dektronics/printalyzer-uvdensitometer/software/firmware/src/state_display.c

#include "state_display.h"

#define LOG_TAG "state_display"

#include <stdbool.h>
#include <math.h>
#include <elog.h>

#include "keypad.h"
#include "display.h"
#include "light.h"
#include "task_sensor.h"
#include "densitometer.h"
#include "settings.h"
#include "util.h"

typedef struct {
    state_t base;
    bool vis_uv;
    bool display_dirty;
    bool light_dirty;
    bool is_detect_prev;
    bool light_idle_on;
    uint32_t light_idle_timeout;
    uint32_t light_idle_off_ticks;
    bool menu_pending;
    int up_repeat;
    int down_repeat;
    state_identifier_t measure_state;
    state_identifier_t alternate_state;
    densitometer_t *densitometer;
    const char *display_title;
    display_mode_t display_mode;
} state_display_t;

static void state_display_entry(state_t *state_base, state_controller_t *controller, state_identifier_t prev_state);
static void state_reflection_display_entry(state_t *state_base, state_controller_t *controller, state_identifier_t prev_state);
static void state_transmission_display_entry(state_t *state_base, state_controller_t *controller, state_identifier_t prev_state);

static void state_display_process(state_t *state_base, state_controller_t *controller);

static state_display_t state_vis_reflection_display_data = {
    .base = {
        .state_entry = state_reflection_display_entry,
        .state_process = state_display_process,
        .state_exit = NULL
    },
    .vis_uv = true,
    .display_dirty = true,
    .light_dirty = true,
    .is_detect_prev = false,
    .light_idle_on = false,
    .light_idle_timeout = 0,
    .light_idle_off_ticks = 0,
    .menu_pending = false,
    .up_repeat = 0,
    .down_repeat = 0,
    .measure_state = STATE_VIS_REFLECTION_MEASURE,
    .alternate_state = STATE_VIS_TRANSMISSION_DISPLAY,
    .densitometer = NULL,
    .display_title = "Reflection",
    .display_mode = DISPLAY_MODE_VIS_REFLECTION
};

static state_display_t state_vis_transmission_display_data = {
    .base = {
        .state_entry = state_transmission_display_entry,
        .state_process = state_display_process,
        .state_exit = NULL
    },
    .vis_uv = true,
    .display_dirty = true,
    .light_dirty = true,
    .is_detect_prev = false,
    .light_idle_on = false,
    .light_idle_timeout = 0,
    .light_idle_off_ticks = 0,
    .menu_pending = false,
    .up_repeat = 0,
    .down_repeat = 0,
    .measure_state = STATE_VIS_TRANSMISSION_MEASURE,
    .alternate_state = STATE_UV_TRANSMISSION_DISPLAY,
    .densitometer = NULL,
    .display_title = "Transmission",
    .display_mode = DISPLAY_MODE_VIS_TRANSMISSION
};

static state_display_t state_uv_transmission_display_data = {
    .base = {
        .state_entry = state_transmission_display_entry,
        .state_process = state_display_process,
        .state_exit = NULL
    },
    .vis_uv = false,
    .display_dirty = true,
    .light_dirty = true,
    .is_detect_prev = false,
    .light_idle_on = false,
    .light_idle_timeout = 0,
    .light_idle_off_ticks = 0,
    .menu_pending = false,
    .up_repeat = 0,
    .down_repeat = 0,
    .measure_state = STATE_UV_TRANSMISSION_MEASURE,
    .alternate_state = STATE_VIS_REFLECTION_DISPLAY,
    .densitometer = NULL,
    .display_title = "Transmission",
    .display_mode = DISPLAY_MODE_UV_TRANSMISSION
};

state_t *state_vis_reflection_display()
{
    return (state_t *)&state_vis_reflection_display_data;
}

state_t *state_vis_transmission_display()
{
    return (state_t *)&state_vis_transmission_display_data;
}

state_t *state_uv_transmission_display()
{
    return (state_t *)&state_uv_transmission_display_data;
}

void state_display_entry(state_t *state_base, state_controller_t *controller, state_identifier_t prev_state)
{
    state_display_t *state = (state_display_t *)state_base;

    state->display_dirty = true;
    state->light_dirty = true;
    state->is_detect_prev = false;
    state->light_idle_on = false;
    state->light_idle_off_ticks = 0;
    state->menu_pending = false;
    state->up_repeat = 0;
    state->down_repeat = 0;

    settings_user_idle_light_t idle_light;
    settings_get_user_idle_light(&idle_light);
    state->light_idle_timeout = 1000UL * idle_light.timeout;

    state_controller_set_home_state(controller, state_controller_get_current_state(controller));
}

void state_reflection_display_entry(state_t *state_base, state_controller_t *controller, state_identifier_t prev_state)
{
    state_display_entry(state_base, controller, prev_state);

    state_display_t *state = (state_display_t *)state_base;
    state->densitometer = densitometer_vis_reflection();

    if (prev_state == STATE_VIS_REFLECTION_MEASURE) {
        /* Set idle light state upon entry assuming measurement is similar to detect */
        if (state->light_idle_timeout > 0) {
            state->light_idle_on = true;
            state->light_idle_off_ticks = osKernelGetTickCount() + state->light_idle_timeout;
        } else {
            state->light_idle_on = false;
            state->light_idle_off_ticks = 0;
        }
        state->light_dirty = true;
    }
}

void state_transmission_display_entry(state_t *state_base, state_controller_t *controller, state_identifier_t prev_state)
{
    state_display_entry(state_base, controller, prev_state);

    state_display_t *state = (state_display_t *)state_base;
    state->densitometer = state->vis_uv ? densitometer_vis_transmission() : densitometer_uv_transmission();

    if (prev_state == (state->vis_uv ? STATE_VIS_TRANSMISSION_MEASURE : STATE_UV_TRANSMISSION_MEASURE)) {
        /* Set idle light state upon entry assuming measurement is similar to detect */
        if (state->light_idle_timeout > 0) {
            state->light_idle_on = true;
            state->light_idle_off_ticks = osKernelGetTickCount() + state->light_idle_timeout;
        } else {
            state->light_idle_on = false;
            state->light_idle_off_ticks = 0;
        }
        state->light_dirty = true;
    }
}

void state_display_process(state_t *state_base, state_controller_t *controller)
{
    state_display_t *state = (state_display_t *)state_base;
    bool is_detect = keypad_is_detect();

    /* Update idle light properties based on a detect switch change */
    if (is_detect != state->is_detect_prev) {
        state->is_detect_prev = is_detect;

        if (is_detect && !state->light_idle_on) {
            state->light_idle_on = true;
            state->light_idle_off_ticks = 0;
            state->light_dirty = true;
        } else if (!is_detect && state->light_idle_on) {
            if (state->light_idle_timeout > 0) {
                state->light_idle_off_ticks = osKernelGetTickCount() + state->light_idle_timeout;
            } else {
                state->light_idle_on = false;
                state->light_idle_off_ticks = 0;
            }
            state->light_dirty = true;
        }
    }

    /* Check for idle light timeout */
    if (state->light_idle_on && state->light_idle_off_ticks > 0
        && TIME_AFTER(osKernelGetTickCount(), state->light_idle_off_ticks)) {
        state->light_idle_on = false;
        state->light_idle_off_ticks = 0;
        state->light_dirty = true;
    }

    /* Apply idle light change */
    if (state->light_dirty) {
        densitometer_set_idle_light(state->densitometer, state->light_idle_on);
        state->light_dirty = false;
    }

    keypad_event_t keypad_event;
    if (keypad_wait_for_event(&keypad_event, STATE_KEYPAD_WAIT) == osOK) {
        state->display_dirty = true;

        if (state->menu_pending) {
            if ((keypad_event.keypad_state & (KEYPAD_BUTTON_UP | KEYPAD_BUTTON_DOWN)) == 0) {
                state->menu_pending = false;
                state_controller_set_next_state(controller, STATE_MAIN_MENU);
            }
        } else {
            if (is_detect && keypad_is_only_key_pressed(&keypad_event, KEYPAD_BUTTON_ACTION)) {
                state_controller_set_next_state(controller, state->measure_state);
            } else if (keypad_event.key == KEYPAD_BUTTON_UP) {
                if (keypad_event.pressed || keypad_event.repeated) {
                    if (state->up_repeat < 5) {
                        state->up_repeat++;
                    } else if (state->up_repeat == 5) {
                        log_i("Clear zero measurement");
                        densitometer_set_zero_d(state->densitometer, NAN);
                        state->up_repeat++;
                        state->display_dirty = true;
                    }
                } else {
                    state->up_repeat = 0;
                    state->display_dirty = true;
                }
            } else if (keypad_event.key == KEYPAD_BUTTON_DOWN) {
                if (keypad_event.pressed || keypad_event.repeated) {
                    if (state->down_repeat < 5) {
                        state->down_repeat++;
                    } else if (state->down_repeat == 5) {
                        log_i("Setting zero measurement");
                        float last_reading = densitometer_get_reading_d(state->densitometer);
                        densitometer_set_zero_d(state->densitometer, last_reading);
                        state->down_repeat++;
                        state->display_dirty = true;
                    }
                } else {
                    state->down_repeat = 0;
                    state->display_dirty = true;
                }
            } else if (keypad_is_only_key_pressed(&keypad_event, KEYPAD_BUTTON_MENU)) {
                state_controller_set_next_state(controller, state->alternate_state);
            }

            if (keypad_is_key_combo_pressed(&keypad_event, KEYPAD_BUTTON_UP, KEYPAD_BUTTON_DOWN)) {
                state->menu_pending = true;
                state->up_repeat = 0;
                state->down_repeat = 0;
            }
        }
    }

    if (state->display_dirty) {
        settings_user_display_format_t display_format;
        settings_get_user_display_format(&display_format);

        float reading;
        if (display_format.unit == SETTING_DISPLAY_UNIT_FSTOP) {
            reading = densitometer_get_display_f(state->densitometer);
        } else {
            reading = densitometer_get_display_d(state->densitometer);
        }

        char sep = settings_get_decimal_separator();
        bool has_zero = !isnan(densitometer_get_zero_d(state->densitometer));
        display_main_elements_t elements = {
            .title = state->display_title,
            .mode = state->display_mode,
            .density100 = ((!isnan(reading)) ? lroundf(reading * 100) : 0),
            .decimal_sep = sep,
            .zero_indicator = has_zero,
            .f_indicator = (display_format.unit == SETTING_DISPLAY_UNIT_FSTOP)
        };

        display_draw_main_elements(&elements);
        state->display_dirty = false;
    }
}
