dektronics/printalyzer-uvdensitometer/software/firmware/src/task_sensor.h

/*
 * Sensor task that runs the TSL2591 light sensor, and controls the LEDs
 * used for making measurements with the sensor.
 */

#ifndef TASK_SENSOR_H
#define TASK_SENSOR_H

#include <cmsis_os.h>

#include "stm32l0xx_hal.h"
#include "tsl2585.h"
#include "sensor.h"

/**
 * Start the sensor task.
 *
 * @param argument The osSemaphoreId_t used to synchronize task startup.
 */
void task_sensor_run(void *argument);

/**
 * Check if the sensor has been successfully initialized.
 */
bool sensor_is_initialized();

/**
 * Enable the sensor.
 */
osStatus_t sensor_start();

/**
 * Disable the sensor.
 */
osStatus_t sensor_stop();

/**
 * Set the sensor's spectrum measurement mode
 *
 * This configures the photodiodes on the sensor to determine which
 * elements will contribute to the output.
 *
 * Note: Switching between single and dual modulator modes must be done
 * before starting the sensor to fully take effect.
 *
 * @param mode Sensor spectrum selection
 */
osStatus_t sensor_set_mode(sensor_mode_t mode);

/**
 * Set the sensor's triggering mode
 *
 * This configures how the sensor's integration cycle is triggered.
 * If the VSYNC mode is selected, then sensor measurements must be
 * triggerred explicitly.
 *
 * @param trigger_mode Sensor trigger mode
 */
osStatus_t sensor_set_trigger_mode(tsl2585_trigger_mode_t trigger_mode);

/**
 * Set the sensor's gain and integration time
 *
 * This function is a wrapper around 'sensor_set_gain()' and
 * 'sensor_set_integration()' for the most common use cases.
 *
 * @param gain Sensor ADC gain
 * @param sample_time Duration of each sample in an integration cycle
 * @param sample_count Number of samples in an integration cycle
 */
osStatus_t sensor_set_config(tsl2585_gain_t gain, uint16_t sample_time, uint16_t sample_count);

/**
 * Set the sensor's gain
 *
 * @param gain Sensor ADC gain
 * @param mod Modulator to apply the gain setting to
 */
osStatus_t sensor_set_gain(tsl2585_gain_t gain, tsl2585_modulator_t mod);

/**
 * Set the sensor's integration time
 *
 * The sample time and count are combined to form the integration time,
 * according to the following formula:
 * TIME(μs) = (sample_count + 1) * (sample_time + 1) * 1.388889μs
 *
 * @param sample_time Duration of each sample in an integration cycle
 * @param sample_count Number of samples in an integration cycle
 */
osStatus_t sensor_set_integration(uint16_t sample_time, uint16_t sample_count);

/**
 * Enable the sensor's automatic gain control
 *
 * @param sample_count Number of samples in an AGC integration cycle
 */
osStatus_t sensor_set_agc_enabled(uint16_t sample_count);

/**
 * Disable the sensor's automatic gain control
 */
osStatus_t sensor_set_agc_disabled();

/**
 * Change the state of the sensor read light sources.
 *
 * All lights are treated as mutually exclusive and are never turned on at
 * the same time. Turning one on will result in the rest being turned off.
 * However, for convenience, it is possible to turn them all off by passing
 * SENSOR_LIGHT_OFF as the light selection.
 *
 * @param light Which light to change
 * @param next_cycle Whether to delay the change until the completion of the next integration cycle
 * @param value Value to set when making the change
 */
osStatus_t sensor_set_light_mode(sensor_light_t light, bool next_cycle, uint16_t value);

/**
 * Explicitly trigger the next sensor integration cycle.
 *
 * For this function to work, the trigger mode must be set to VSYNC.
 */
osStatus_t sensor_trigger_next_reading();

/**
 * Get the next reading from the sensor.
 * If no reading is currently available, then this function will block
 * until the completion of the next sensor integration cycle.
 *
 * @param reading Sensor reading data
 * @param timeout Amount of time to wait for a reading to become available
 * @return osOK on success, osErrorTimeout on timeout
 */
osStatus_t sensor_get_next_reading(sensor_reading_t *reading, uint32_t timeout);

/**
* Get the current sensor head temperature reading.
*
* This function does not depend on the state of the light sensor,
* and can be called at any time after this task is initialized.
*
* @param temp_c Current sensor head temperature in Celsius
*/
osStatus_t sensor_read_temperature(float *temp_c);

/**
 * Sensor interrupt handler.
 */
void sensor_int_handler();

#endif /* TASK_SENSOR_H */
