dektronics/printalyzer-uvdensitometer/software/firmware/src/state_display.h

#ifndef STATE_DISPLAY_H
#define STATE_DISPLAY_H

#include "state_controller.h"

state_t *state_vis_reflection_display();
state_t *state_vis_transmission_display();
state_t *state_uv_transmission_display();

#endif /* STATE_DISPLAY_H */
