dektronics/printalyzer-uvdensitometer/software/firmware/src/state_measure.h

#ifndef STATE_MEASURE_H
#define STATE_MEASURE_H

#include "state_controller.h"

state_t *state_vis_reflection_measure();
state_t *state_vis_transmission_measure();
state_t *state_uv_transmission_measure();

#endif /* STATE_MEASURE_H */
