dektronics/printalyzer-uvdensitometer/software/firmware/src/display_assets.c

#include "display_assets.h"

#include <string.h>

#define asset_reflection_40_width 40
#define asset_reflection_40_height 40
static const unsigned char asset_reflection_40_bits[] = {
    0x00, 0x00, 0x3c, 0x00, 0x00, 0x00, 0x00, 0x3c, 0x00, 0x00, 0x00, 0x00,
    0x3c, 0x00, 0x00, 0x00, 0x00, 0x3c, 0x00, 0x00, 0x00, 0x00, 0x3c, 0x00,
    0x00, 0x00, 0xc0, 0xff, 0x03, 0x00, 0x00, 0xf0, 0xff, 0x0f, 0x00, 0x00,
    0xf8, 0xff, 0x1f, 0x00, 0x00, 0xfe, 0x3c, 0x7f, 0x00, 0x00, 0x3f, 0x3c,
    0xfc, 0x00, 0x00, 0x0f, 0x3c, 0xf0, 0x00, 0x80, 0x07, 0x3c, 0xe0, 0x01,
    0xc0, 0x03, 0x00, 0xc0, 0x03, 0xc0, 0x03, 0x00, 0xc0, 0x03, 0xe0, 0x01,
    0x00, 0x80, 0x07, 0xe0, 0x01, 0x00, 0x80, 0x07, 0xe0, 0x00, 0x00, 0x00,
    0x07, 0xe0, 0x00, 0x00, 0x00, 0x07, 0xff, 0x0f, 0x18, 0xf0, 0xff, 0xff,
    0x0f, 0x3c, 0xf0, 0xff, 0xff, 0x0f, 0x3c, 0xf0, 0xff, 0xff, 0x0f, 0x18,
    0xf0, 0xff, 0xe0, 0x00, 0x00, 0x00, 0x07, 0xe0, 0x00, 0x00, 0x00, 0x07,
    0xe0, 0x01, 0x00, 0x80, 0x07, 0xe0, 0x01, 0x00, 0x80, 0x07, 0xc0, 0x03,
    0x00, 0xc0, 0x03, 0xc0, 0x03, 0x00, 0xc0, 0x03, 0x80, 0x07, 0x3c, 0xe0,
    0x01, 0x00, 0x0f, 0x3c, 0xf0, 0x00, 0x00, 0x3f, 0x3c, 0xfc, 0x00, 0x00,
    0xfe, 0x3c, 0x7f, 0x00, 0x00, 0xf8, 0xff, 0x1f, 0x00, 0x00, 0xf0, 0xff,
    0x0f, 0x00, 0x00, 0xc0, 0xff, 0x03, 0x00, 0x00, 0x00, 0x3c, 0x00, 0x00,
    0x00, 0x00, 0x3c, 0x00, 0x00, 0x00, 0x00, 0x3c, 0x00, 0x00, 0x00, 0x00,
    0x3c, 0x00, 0x00, 0x00, 0x00, 0x3c, 0x00, 0x00 };

#define asset_reflection_40_1_width 40
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
    0xfe, 0x00, 0x7f, 0x00, 0x00, 0xf8, 0xff, 0x1f, 0x00, 0x00, 0xf0, 0xff,
    0x0f, 0x00, 0x00, 0xc0, 0xff, 0x03, 0x00, 0x00, 0x00, 0x00, 0x00, 0x00,
    0x00, 0x00, 0x00, 0x00, 0x00, 0x00, 0x00, 0x00, 0x00, 0x00, 0x00, 0x00,
    0x00, 0x00, 0x00, 0x00, 0x00, 0x00, 0x00, 0x00 };

#define asset_vis_icon_width 16
#define asset_vis_icon_height 11
static unsigned char asset_vis_icon_bits[] = {
    0xfe, 0x7f, 0xff, 0xff, 0xbb, 0xc6, 0xbb, 0xfa, 0x93, 0xfa, 0xd7, 0xe2,
    0xc7, 0xde, 0xef, 0xde, 0xef, 0xe2, 0xff, 0xff, 0xfe, 0x7f };

#define asset_uv_icon_width 16
#define asset_uv_icon_height 11
static unsigned char asset_uv_icon_bits[] = {
    0xfe, 0x7f, 0xff, 0xff, 0xbb, 0xdd, 0xbb, 0xdd, 0xbb, 0xc9, 0xbb, 0xeb,
    0xbb, 0xe3, 0xbb, 0xf7, 0xc7, 0xf7, 0xff, 0xff, 0xfe, 0x7f };

#define asset_zero_indicator_width 10
#define asset_zero_indicator_height 12
static unsigned char asset_zero_indicator_bits[] = {
    0x78, 0x00, 0x78, 0x00, 0x78, 0x00, 0x78, 0x00, 0x78, 0x00, 0xff, 0x03,
    0xfe, 0x01, 0xfc, 0x00, 0x78, 0x00, 0x30, 0x00, 0xff, 0x03, 0xff, 0x03 };
#define ASSET_ENTRY(x) { x##_bits, x##_width, x##_height }

static const asset_info_t asset_list[] = {
    ASSET_ENTRY(asset_reflection_40),
    ASSET_ENTRY(asset_reflection_40_1),
    ASSET_ENTRY(asset_reflection_40_2),
    ASSET_ENTRY(asset_transmission_40),
    ASSET_ENTRY(asset_transmission_40_1),
    ASSET_ENTRY(asset_transmission_40_2),
    ASSET_ENTRY(asset_vis_icon),
    ASSET_ENTRY(asset_uv_icon),
    ASSET_ENTRY(asset_zero_indicator)
};

uint8_t display_asset_get(asset_info_t *asset_info, asset_name_t asset_name)
{
    if (asset_info && asset_name >= 0 && asset_name < ASSET_MAX) {
        memcpy(asset_info, &asset_list[asset_name], sizeof(asset_info_t));
        return 1;
    } else {
        return 0;
    }
}
