dektronics/printalyzer-uvdensitometer/software/firmware/src/cdc_handler.c

#include "cdc_handler.h"

#define LOG_TAG "cdc_handler"
#include <elog.h>
#include <elog_port.h>

#include "stm32l0xx_hal.h"

#include <printf.h>
#include <stdlib.h>
#include <string.h>
#include <ctype.h>
#include <machine/endian.h>
#include <math.h>
#include <tusb.h>
#include <cmsis_os.h>
#include <FreeRTOS.h>

#include "settings.h"
#include "display.h"
#include "light.h"
#include "sensor.h"
#include "task_main.h"
#include "task_sensor.h"
#include "adc_handler.h"
#include "densitometer.h"
#include "app_descriptor.h"
#include "util.h"
#include "keypad.h"

#define CMD_DATA_SIZE 104
#define CDC_TX_TIMEOUT 200
#define CDC_MIN_BIT_RATE 9600

typedef enum {
    CMD_TYPE_SET,
    CMD_TYPE_GET,
    CMD_TYPE_INVOKE
} cmd_type_t;

typedef enum {
    CMD_CATEGORY_SYSTEM,
    CMD_CATEGORY_MEASUREMENT,
    CMD_CATEGORY_CALIBRATION,
    CMD_CATEGORY_DIAGNOSTICS
} cmd_category_t;

typedef struct {
    cmd_type_t type;
    cmd_category_t category;
    char action[8];
    char args[96];
} cdc_command_t;

typedef enum {
    READING_FORMAT_BASIC,
    READING_FORMAT_EXT
} cdc_reading_format_t;

static volatile bool cdc_initialized = false;
static volatile bool cdc_host_connected = false;
static volatile bool cdc_logging_redirected = false;
static uint8_t cmd_buffer[CMD_DATA_SIZE];
static size_t cmd_buffer_len = 0;
static bool cdc_remote_enabled = false;
static volatile bool cdc_remote_active = false;
static volatile bool cdc_remote_sensor_active = false;
static cdc_reading_format_t reading_format = READING_FORMAT_BASIC;

/* Semaphore used to unblock the task when new data is available */
static osSemaphoreId_t cdc_rx_semaphore = NULL;
static const osSemaphoreAttr_t cdc_rx_semaphore_attrs = {
    .name = "cdc_rx_semaphore"
};

/* Semaphore used to synchronize data writing */
static osSemaphoreId_t cdc_tx_semaphore = NULL;
static const osSemaphoreAttr_t cdc_tx_semaphore_attrs = {
    .name = "cdc_tx_semaphore"
};

/* Mutex used to allow CDC writes from different tasks */
static osMutexId_t cdc_mutex = NULL;
static const osMutexAttr_t cdc_mutex_attrs = {
    .name = "cdc_mutex"
};

static void cdc_task_loop();
static void cdc_set_connected(bool connected);
static void cdc_process_command(const char *buf, size_t len);
static bool cdc_parse_command(cdc_command_t *cmd, const char *buf, size_t len);
static bool cdc_process_command_system(const cdc_command_t *cmd);
static bool cdc_process_command_measurement(const cdc_command_t *cmd);
static bool cdc_process_command_calibration(const cdc_command_t *cmd);
static bool cdc_invoke_gain_calibration_callback(sensor_gain_calibration_status_t status, int param, void *user_data);
static bool cdc_process_command_diagnostics(const cdc_command_t *cmd);

static void cdc_send_response(const char *str);
static void cdc_send_command_response(const cdc_command_t *cmd, const char *str);

static size_t encode_f32_array_response(char *buf, const float *array, size_t len);
static size_t encode_f32(char *out, float value);
static uint8_t decode_hex_char(char ch, bool *ok);
static float decode_f32(const char *buf);
static size_t decode_f32_array_args(const char *args, float *elements, size_t len);
static size_t decode_u16_array_args(const char *args, uint16_t *elements, size_t len);

extern I2C_HandleTypeDef hi2c1;

void task_cdc_run(void *argument)
{
    osSemaphoreId_t task_start_semaphore = argument;

    log_d("cdc_task start");

    /* Create the CDC RX semaphore */
    cdc_rx_semaphore = osSemaphoreNew(1, 0, &cdc_rx_semaphore_attrs);
    if (!cdc_rx_semaphore) {
        log_e("cdc_rx_semaphore create error");
        return;
    }

    /* Create the CDC TX semaphore */
    cdc_tx_semaphore = osSemaphoreNew(1, 0, &cdc_tx_semaphore_attrs);
    if (!cdc_tx_semaphore) {
        log_e("cdc_tx_semaphore create error");
        return;
    }

    /* Create the CDC write mutex */
    cdc_mutex = osMutexNew(&cdc_mutex_attrs);
    if (!cdc_mutex) {
        log_e("Unable to create cdc_mutex");
        return;
    }

    cdc_initialized = true;

    /* Release the startup semaphore */
    if (osSemaphoreRelease(task_start_semaphore) != osOK) {
        log_e("Unable to release task_start_semaphore");
        return;
    }

    while (1) {
        /* Process data */
        cdc_task_loop();

        /* Block for new data */
        if (osSemaphoreAcquire(cdc_rx_semaphore, portMAX_DELAY) != osOK) {
            log_e("Unable to acquire cdc_rx_semaphore");
        }
    }
}

void tud_cdc_line_state_cb(uint8_t itf, bool dtr, bool rts)
{
    if (!cdc_logging_redirected) {
        log_d("tud_cdc_line_state: itf=%d, dtr=%d, rts=%d", itf, dtr, rts);
    }
    osMutexAcquire(cdc_mutex, portMAX_DELAY);
    if (dtr) {
        cdc_line_coding_t *coding = NULL;
        tud_cdc_get_line_coding(coding);
        cdc_set_connected(!coding || (coding->bit_rate >= CDC_MIN_BIT_RATE));
    } else {
        cdc_set_connected(false);
    }
    osMutexRelease(cdc_mutex);
}

void tud_cdc_line_coding_cb(uint8_t itf, cdc_line_coding_t const* p_line_coding)
{
    if (!cdc_logging_redirected) {
        log_d("tud_cdc_line_coding: itf=%d, bit_rate=%d", itf, p_line_coding->bit_rate);
    }
    osMutexAcquire(cdc_mutex, portMAX_DELAY);
    if (p_line_coding->bit_rate < CDC_MIN_BIT_RATE) {
        log_w("Bit rate not supported: %d < %d", p_line_coding->bit_rate, CDC_MIN_BIT_RATE);
        cdc_set_connected(false);
    }
    osMutexRelease(cdc_mutex);
}

void tud_cdc_tx_complete_cb(uint8_t itf)
{
    /* log_d("tud_cdc_tx_complete_cb: itf=%d", itf); */
    if (!cdc_initialized) { return; }
    osSemaphoreRelease(cdc_tx_semaphore);
}

void tud_cdc_rx_cb(uint8_t itf)
{
    /* log_d("tud_cdc_rx_cb: itf=%d", itf); */
    if (!cdc_initialized) { return; }
    osSemaphoreRelease(cdc_rx_semaphore);
}

void cdc_task_loop()
{
    /*
     * Notes from example:
     * connected() check for DTR bit
     * Most but not all terminal client set this when making connection
     * if ( tud_cdc_connected() )
     */

    if (tud_cdc_available()) {
        /* Read data into local buffer */
        char buf[64];
        uint32_t count = tud_cdc_read(buf, sizeof(buf));

        for (size_t i = 0; i < count; i++) {
            /* Fill buffer as long as there is space */
            if (cmd_buffer_len < CMD_DATA_SIZE) {
                if (buf[i] >= 0x20 && buf[i] < 0x7F) {
                    /* Only fill buffer with printable characters */
                    cmd_buffer[cmd_buffer_len++] = buf[i];
                } else if (buf[i] == 0x08 || buf[i] == 0x7F) {
                    /* Handle backspace behavior */
                    if (cmd_buffer_len > 0) {
                        cmd_buffer_len--;
                        cmd_buffer[cmd_buffer_len] = '\0';
                    }
                }
            }
            /* Accept command as soon as a line break is sent */
            if ((buf[i] == '\r' || buf[i] == '\n') && cmd_buffer_len > 0) {
                /* Accept command */
                cmd_buffer[cmd_buffer_len] = '\0';
                cdc_process_command((const char *)cmd_buffer, cmd_buffer_len);

                /* Clear command buffer */
                memset(cmd_buffer, 0, sizeof(cmd_buffer));
                cmd_buffer_len = 0;
            }
        }
    }
}

void cdc_set_connected(bool connected)
{
    if (cdc_host_connected != connected) {
        if (!connected) {
            elog_port_redirect(NULL);
            elog_set_text_color_enabled(true);
            cdc_logging_redirected = false;
            if (cdc_remote_enabled) {
                task_main_force_state(STATE_HOME);
                cdc_remote_enabled = false;
                cdc_remote_active = false;
                cdc_remote_sensor_active = false;
            }
            reading_format = READING_FORMAT_BASIC;
            densitometer_set_allow_uncalibrated_measurements(false);
        }
        cdc_host_connected = connected;
    }
}

bool cdc_is_connected()
{
    return cdc_host_connected;
}

void cdc_process_command(const char *buf, size_t len)
{
    cdc_command_t cmd = {0};

    if (len == 0 || buf[0] == '\0') {
        return;
    }

    if (cdc_parse_command(&cmd, buf, len)) {
        bool result = false;
        switch (cmd.category) {
        case CMD_CATEGORY_SYSTEM:
            result = cdc_process_command_system(&cmd);
            break;
        case CMD_CATEGORY_MEASUREMENT:
            result = cdc_process_command_measurement(&cmd);
            break;
        case CMD_CATEGORY_CALIBRATION:
            result = cdc_process_command_calibration(&cmd);
            break;
        case CMD_CATEGORY_DIAGNOSTICS:
            result = cdc_process_command_diagnostics(&cmd);
            break;
        default:
            break;
        }
        if (!result) {
            cdc_send_command_response(&cmd, "NAK");
        }
    }
}

bool cdc_parse_command(cdc_command_t *cmd, const char *buf, size_t len)
{
    cmd_type_t type;
    cmd_category_t category;

    if (!cmd || !buf || len < 2 || buf[0] == '\0') {
        return false;
    }

    switch (buf[0]) {
    case 'S':
        type = CMD_TYPE_SET;
        break;
    case 'G':
        type = CMD_TYPE_GET;
        break;
    case 'I':
        type = CMD_TYPE_INVOKE;
        break;
    default:
        return false;
    }

    switch (buf[1]) {
    case 'S':
        category = CMD_CATEGORY_SYSTEM;
        break;
    case 'M':
        category = CMD_CATEGORY_MEASUREMENT;
        break;
    case 'C':
        category = CMD_CATEGORY_CALIBRATION;
        break;
    case 'D':
        category = CMD_CATEGORY_DIAGNOSTICS;
        break;
    default:
        return false;
    }

    if (len > 2 && buf[2] != ' ') {
        return false;
    }

    cmd->type = type;
    cmd->category = category;

    if (len > 3) {
        char *p = strchr(buf + 3, ',');
        if (p) {
            strncpy(cmd->action, buf + 3, MIN(p - (buf + 3), sizeof(cmd->action) - 1));
            strncpy(cmd->args, p + 1, MIN(len - ((p + 1) - buf), sizeof(cmd->args) - 1));
        } else {
            strncpy(cmd->action, buf + 3, MIN(len - 3, sizeof(cmd->action) - 1));
            memset(cmd->args, 0, sizeof(cmd->args));
        }
    } else {
        memset(cmd->action, 0, sizeof(cmd->action));
        memset(cmd->args, 0, sizeof(cmd->args));
    }

    log_i("Command: [%c][%c] {%s},\"%s\"", buf[0], buf[1], cmd->action, cmd->args);

    return true;
}

bool cdc_process_command_system(const cdc_command_t *cmd)
{
    /*
     * System Commands
     * "GS V"    -> Get project name and version
     * "GS B"    -> Get firmware build information
     * "GS DEV"  -> Get device information (HAL version, MCU Rev ID, MCU Dev ID, SysClock)
     * "GS RTOS" -> Get FreeRTOS information
     * "GS UID"  -> Get device unique ID
     * "GS ISEN" -> Internal sensor readings
     * "IS REMOTE,n" -> Invoke remote control mode (enable = 1, disable = 0)
     * "SS DISP,\"text\"" -> Write text to the display [remote]
     * "SS DISP,n" -> Enable or disable the display (enable = 1, disable = 0) [remote]
     */
    const app_descriptor_t *app_descriptor = app_descriptor_get();
    char buf[128];

    if (!cmd) { return false; }

    if (cmd->type == CMD_TYPE_GET && strcmp(cmd->action, "V") == 0) {
        /*
         * Output format:
         * Project name, Version
         */
        sprintf(buf, "\"%s\",\"%s\"", app_descriptor->project_name, app_descriptor->version);
        cdc_send_command_response(cmd, buf);
        return true;
    } else if (cmd->type == CMD_TYPE_GET && strcmp(cmd->action, "B") == 0) {
        /*
         * Output format:
         * Build date, Build describe, Checksum
         */
        sprintf(buf, "\"%s\",\"%s\",%08lX",
            app_descriptor->build_date,
            app_descriptor->build_describe,
            __bswap32(app_descriptor->crc32));
        cdc_send_command_response(cmd, buf);
        return true;
    } else if (cmd->type == CMD_TYPE_GET && strcmp(cmd->action, "DEV") == 0) {
        /*
         * Output format:
         * HAL Version, MCU Device ID, MCU Revision ID, SysClock Frequency
         */
        uint32_t hal_ver = HAL_GetHalVersion();
        uint8_t hal_ver_code = ((uint8_t)(hal_ver)) & 0x0F;

        sprintf(buf, "%d.%d.%d%c,0x%lX,0x%lX,%ldMHz",
            ((uint8_t)(hal_ver >> 24)) & 0x0F,
            ((uint8_t)(hal_ver >> 16)) & 0x0F,
            ((uint8_t)(hal_ver >> 8)) & 0x0F,
            (hal_ver_code > 0 ? (char)hal_ver_code : ' '),
            HAL_GetDEVID(),
            HAL_GetREVID(),
            HAL_RCC_GetSysClockFreq() / 1000000);
        cdc_send_command_response(cmd, buf);
        return true;
    } else if (cmd->type == CMD_TYPE_GET && strcmp(cmd->action, "RTOS") == 0) {
        /*
         * Output format:
         * FreeRTOS Version, Heap Free, Heap Watermark, Task Count
         */
        sprintf(buf, "%s,%d,%d,%ld",
            tskKERNEL_VERSION_NUMBER,
            xPortGetFreeHeapSize(), xPortGetMinimumEverFreeHeapSize(),
            uxTaskGetNumberOfTasks());
        cdc_send_command_response(cmd, buf);
        return true;
    } else if (cmd->type == CMD_TYPE_GET && strcmp(cmd->action, "UID") == 0) {
        sprintf(buf, "%08lX%08lX%08lX",
            __bswap32(HAL_GetUIDw0()),
            __bswap32(HAL_GetUIDw1()),
            __bswap32(HAL_GetUIDw2()));
        cdc_send_command_response(cmd, buf);
        return true;
    } else if (cmd->type == CMD_TYPE_GET && strcmp(cmd->action, "ISEN") == 0) {
        /*
         * Output format:
         * VDDA, Temperature (MCU), Temperature (Sensor)
         */
        adc_readings_t readings = {0};
        float sensor_temp_c = 0;

        adc_read(&readings);
        sensor_read_temperature(&sensor_temp_c);

        sprintf_(buf, "%dmV,%.1fC,%.1fC", readings.vdda_mv, readings.temp_c, sensor_temp_c);
        cdc_send_command_response(cmd, buf);

        return true;
    } else if (cmd->type == CMD_TYPE_INVOKE && strcmp(cmd->action, "REMOTE") == 0) {
        bool enable;
        if (cmd->args[0] == '0' && cmd->args[1] == '\0') {
            enable = false;
        } else if (cmd->args[0] == '1' && cmd->args[1] == '\0') {
            enable = true;
        } else {
            return false;
        }

        log_i("Set remote control mode: %d", enable);
        if (enable) {
            cdc_remote_enabled = true;
            task_main_force_state(STATE_REMOTE);
        } else {
            task_main_force_state(STATE_HOME);
            cdc_remote_enabled = false;
        }

        return true;
    } else if (cmd->type == CMD_TYPE_SET && strcmp(cmd->action, "DISP") == 0 && cdc_remote_active) {
        if (cmd->args[0] == '"') {
            memset(buf, 0, sizeof(buf));
            uint8_t j = 0;
            for (uint8_t i = 1; i < 56; i++) {
                if (i < 55 && cmd->args[i] == '\\' && cmd->args[i + 1] == 'n') {
                    buf[j++] = '\n';
                    i++;
                } else if (i < 55 && cmd->args[i] == '\\' && cmd->args[i + 1] == '\\') {
                    buf[j++] = '\\';
                    i++;
                } else {
                    buf[j++] = cmd->args[i];
                }
            }

            size_t len = strlen(buf);
            if (len > 0 && buf[len - 1] == '"') {
                buf[len - 1] = '\0';
            }

            display_static_message(buf);
        } else if (cmd->args[0] == '0' && cmd->args[1] == '\0') {
            display_enable(false);
        } else if (cmd->args[0] == '1' && cmd->args[1] == '\0') {
            display_enable(true);
        } else {
            return false;
        }

        cdc_send_command_response(cmd, "OK");
        return true;
    } else {
        return false;
    }
}

bool cdc_process_command_measurement(const cdc_command_t *cmd)
{
    /*
     * Measurement Commands
     * "GM REFL" -> Get last reflection measurement
     * "GM TRAN" -> Get last transmission measurement
     * "SM FORMAT,x" -> Set measurement data format ("BASIC", "EXT")
     * "SM UNCAL,x" -> Allow uncalibrated readings (0=false, 1=true)
     */
    if (cmd->type == CMD_TYPE_GET && strcmp(cmd->action, "REFL") == 0) {
        char buf[32];
        float reading = densitometer_get_display_d(densitometer_vis_reflection());
        encode_f32(buf, reading);
        cdc_send_command_response(cmd, buf);
        return true;
    } else if (cmd->type == CMD_TYPE_GET && strcmp(cmd->action, "TRAN") == 0) {
        char buf[32];
        float reading = densitometer_get_display_d(densitometer_vis_transmission());
        encode_f32(buf, reading);
        cdc_send_command_response(cmd, buf);
        return true;
    } else if (cmd->type == CMD_TYPE_GET && strcmp(cmd->action, "UVTR") == 0) {
        char buf[32];
        float reading = densitometer_get_display_d(densitometer_uv_transmission());
        encode_f32(buf, reading);
        cdc_send_command_response(cmd, buf);
        return true;
    } else if (cmd->type == CMD_TYPE_SET && strcmp(cmd->action, "FORMAT") == 0) {
        if (strcmp(cmd->args, "BASIC") == 0) {
            reading_format = READING_FORMAT_BASIC;
        } else if (strcmp(cmd->args, "EXT") == 0) {
            reading_format = READING_FORMAT_EXT;
        } else {
            return false;
        }
        cdc_send_command_response(cmd, "OK");
        return true;
    } else if (cmd->type == CMD_TYPE_SET && strcmp(cmd->action, "UNCAL") == 0) {
        if (strcmp(cmd->args, "0") == 0) {
            densitometer_set_allow_uncalibrated_measurements(false);
        } else if (strcmp(cmd->args, "1") == 0) {
            densitometer_set_allow_uncalibrated_measurements(true);
        } else {
            return false;
        }
        cdc_send_command_response(cmd, "OK");
        return true;
    }
    return false;
}

bool cdc_process_command_calibration(const cdc_command_t *cmd)
{
    /*
     * Calibration Commands
     * "IC GAIN" -> Invoke the sensor gain calibration process [remote]
     * "GC GAIN" -> Get sensor gain calibration values
     * "SC GAIN" -> Set sensor gain calibration values
     * "GC SLOPE" -> Get sensor slope calibration values
     * "SC SLOPE" -> Set sensor slope calibration values
     * "GC VTEMP" -> Get VIS sensor temperature calibration values
     * "SC VTEMP" -> Set VIS sensor temperature calibration values
     * "GC UTEMP" -> Get VIS sensor temperature calibration values
     * "SC UTEMP" -> Set VIS sensor temperature calibration values
     * "GC REFL" -> Get VIS reflection density calibration values
     * "SC REFL" -> Set VIS reflection density calibration values
     * "GC TRAN" -> Get VIS transmission density calibration values
     * "SC TRAN" -> Set VIS transmission density calibration values
     * "GC UVTR" -> Get UV transmission density calibration values
     * "SC UVTR" -> Set UV transmission density calibration values
     */
    if (cmd->type == CMD_TYPE_INVOKE && strcmp(cmd->action, "GAIN") == 0 && cdc_remote_active) {
        osStatus_t result = sensor_gain_calibration(cdc_invoke_gain_calibration_callback, (void *)cmd);
        if (result == osOK) {
            cdc_send_command_response(cmd, "OK");
        } else {
            cdc_send_command_response(cmd, "ERR");
        }
        return true;
    }
#ifdef TEST_LIGHT_CAL
    else if (cmd->type == CMD_TYPE_INVOKE && strcmp(cmd->action, "LR") == 0 && cdc_remote_active) {
        /* This command is only enabled for development and testing purposes */
        osStatus_t result = sensor_light_calibration(SENSOR_LIGHT_VIS_REFLECTION);
        if (result == osOK) {
            cdc_send_command_response(cmd, "OK");
        } else {
            cdc_send_command_response(cmd, "ERR");
        }
        return true;
    } else if (cmd->type == CMD_TYPE_INVOKE && strcmp(cmd->action, "LT") == 0 && cdc_remote_active) {
        /* This command is only enabled for development and testing purposes */
        osStatus_t result = sensor_light_calibration(SENSOR_LIGHT_VIS_TRANSMISSION);
        if (result == osOK) {
            cdc_send_command_response(cmd, "OK");
        } else {
            cdc_send_command_response(cmd, "ERR");
        }
        return true;
    } else if (cmd->type == CMD_TYPE_INVOKE && strcmp(cmd->action, "LTU") == 0 && cdc_remote_active) {
        /* This command is only enabled for development and testing purposes */
        osStatus_t result = sensor_light_calibration(SENSOR_LIGHT_UV_TRANSMISSION);
        if (result == osOK) {
            cdc_send_command_response(cmd, "OK");
        } else {
            cdc_send_command_response(cmd, "ERR");
        }
        return true;
    }
#endif
    else if (cmd->type == CMD_TYPE_GET && strcmp(cmd->action, "GAIN") == 0) {
        char buf[128];
        settings_cal_gain_t cal_gain;

        settings_get_cal_gain(&cal_gain);

        encode_f32_array_response(buf, cal_gain.values, TSL2585_GAIN_256X + 1);

        cdc_send_command_response(cmd, buf);
        return true;
    } else if (cmd->type == CMD_TYPE_SET && strcmp(cmd->action, "GAIN") == 0) {
        float gain_val[10] = {0};
        size_t n = decode_f32_array_args(cmd->args, gain_val, 10);
        if (n == 10) {
            settings_cal_gain_t cal_gain = {0};

            for (size_t i = 0; i < 10; i++) {
                cal_gain.values[i] = gain_val[i];
            }

            if (settings_set_cal_gain(&cal_gain)) {
                cdc_send_command_response(cmd, "OK");
            } else {
                cdc_send_command_response(cmd, "ERR");
            }

            return true;
        }
    } else if (cmd->type == CMD_TYPE_GET && strcmp(cmd->action, "VTEMP") == 0) {
        char buf[64];
        settings_cal_temperature_t cal_temperature;
        float temp_val[3] = {0};

        settings_get_cal_vis_temperature(&cal_temperature);
        temp_val[0] = cal_temperature.b0;
        temp_val[1] = cal_temperature.b1;
        temp_val[2] = cal_temperature.b2;
        encode_f32_array_response(buf, temp_val, 3);

        cdc_send_command_response(cmd, buf);
        return true;
    } else if (cmd->type == CMD_TYPE_SET && strcmp(cmd->action, "VTEMP") == 0) {
        float temp_val[3] = {0};
        const size_t n = decode_f32_array_args(cmd->args, temp_val, 3);
        if (n == 3) {
            settings_cal_temperature_t cal_temperature = {0};
            cal_temperature.b0 = temp_val[0];
            cal_temperature.b1 = temp_val[1];
            cal_temperature.b2 = temp_val[2];

            if (settings_set_cal_vis_temperature(&cal_temperature)) {
                cdc_send_command_response(cmd, "OK");
            } else {
                cdc_send_command_response(cmd, "ERR");
            }
            return true;
        }
    } else if (cmd->type == CMD_TYPE_GET && strcmp(cmd->action, "UTEMP") == 0) {
        char buf[64];
        settings_cal_temperature_t cal_temperature;
        float temp_val[3] = {0};

        settings_get_cal_uv_temperature(&cal_temperature);
        temp_val[0] = cal_temperature.b0;
        temp_val[1] = cal_temperature.b1;
        temp_val[2] = cal_temperature.b2;
        encode_f32_array_response(buf, temp_val, 3);

        cdc_send_command_response(cmd, buf);
        return true;
    } else if (cmd->type == CMD_TYPE_SET && strcmp(cmd->action, "UTEMP") == 0) {
        float temp_val[3] = {0};
        const size_t n = decode_f32_array_args(cmd->args, temp_val, 3);
        if (n == 3) {
            settings_cal_temperature_t cal_temperature = {0};
            cal_temperature.b0 = temp_val[0];
            cal_temperature.b1 = temp_val[1];
            cal_temperature.b2 = temp_val[2];

            if (settings_set_cal_uv_temperature(&cal_temperature)) {
                cdc_send_command_response(cmd, "OK");
            } else {
                cdc_send_command_response(cmd, "ERR");
            }
            return true;
        }
    } else if (cmd->type == CMD_TYPE_GET && strcmp(cmd->action, "REFL") == 0) {
        char buf[64];
        settings_cal_reflection_t cal_reflection;
        float refl_val[4] = {0};

        settings_get_cal_vis_reflection(&cal_reflection);
        refl_val[0] = cal_reflection.lo_d;
        refl_val[1] = cal_reflection.lo_value;
        refl_val[2] = cal_reflection.hi_d;
        refl_val[3] = cal_reflection.hi_value;

        encode_f32_array_response(buf, refl_val, 4);

        cdc_send_command_response(cmd, buf);
        return true;
    } else if (cmd->type == CMD_TYPE_SET && strcmp(cmd->action, "REFL") == 0) {
        float refl_val[4] = {0};
        size_t n = decode_f32_array_args(cmd->args, refl_val, 4);
        if (n == 4) {
            settings_cal_reflection_t cal_reflection = {0};
            cal_reflection.lo_d = refl_val[0];
            cal_reflection.lo_value = refl_val[1];
            cal_reflection.hi_d = refl_val[2];
            cal_reflection.hi_value = refl_val[3];

            if (settings_set_cal_vis_reflection(&cal_reflection)) {
                cdc_send_command_response(cmd, "OK");
            } else {
                cdc_send_command_response(cmd, "ERR");
            }

            return true;
        }
    } else if (cmd->type == CMD_TYPE_GET && strcmp(cmd->action, "TRAN") == 0) {
        char buf[64];
        settings_cal_transmission_t cal_transmission;
        float tran_val[4] = {0};

        settings_get_cal_vis_transmission(&cal_transmission);
        tran_val[0] = 0.0F;
        tran_val[1] = cal_transmission.zero_value;
        tran_val[2] = cal_transmission.hi_d;
        tran_val[3] = cal_transmission.hi_value;

        encode_f32_array_response(buf, tran_val, 4);

        cdc_send_command_response(cmd, buf);
        return true;
    } else if (cmd->type == CMD_TYPE_SET && strcmp(cmd->action, "TRAN") == 0) {
        float tran_val[4] = {0};
        size_t n = decode_f32_array_args(cmd->args, tran_val, 4);
        if (n == 4 && tran_val[0] < 0.001F) {
            settings_cal_transmission_t cal_transmission = {0};
            cal_transmission.zero_value = tran_val[1];
            cal_transmission.hi_d = tran_val[2];
            cal_transmission.hi_value = tran_val[3];

            if (settings_set_cal_vis_transmission(&cal_transmission)) {
                cdc_send_command_response(cmd, "OK");
            } else {
                cdc_send_command_response(cmd, "ERR");
            }

            return true;
        }
    } else if (cmd->type == CMD_TYPE_GET && strcmp(cmd->action, "UVTR") == 0) {
        char buf[64];
        settings_cal_transmission_t cal_transmission;
        float tran_val[4] = {0};

        settings_get_cal_uv_transmission(&cal_transmission);
        tran_val[0] = 0.0F;
        tran_val[1] = cal_transmission.zero_value;
        tran_val[2] = cal_transmission.hi_d;
        tran_val[3] = cal_transmission.hi_value;

        encode_f32_array_response(buf, tran_val, 4);

        cdc_send_command_response(cmd, buf);
        return true;
    } else if (cmd->type == CMD_TYPE_SET && strcmp(cmd->action, "UVTR") == 0) {
        float tran_val[4] = {0};
        size_t n = decode_f32_array_args(cmd->args, tran_val, 4);
        if (n == 4 && tran_val[0] < 0.001F) {
            settings_cal_transmission_t cal_transmission = {0};
            cal_transmission.zero_value = tran_val[1];
            cal_transmission.hi_d = tran_val[2];
            cal_transmission.hi_value = tran_val[3];

            if (settings_set_cal_uv_transmission(&cal_transmission)) {
                cdc_send_command_response(cmd, "OK");
            } else {
                cdc_send_command_response(cmd, "ERR");
            }

            return true;
        }
    }

    return false;
}

bool cdc_invoke_gain_calibration_callback(sensor_gain_calibration_status_t status, int param, void *user_data)
{
    const cdc_command_t *cmd = (const cdc_command_t *)user_data;
    char buf[32];
    sprintf(buf, "STATUS,%d,%d", status, param);
    cdc_send_command_response(cmd, buf);

    return keypad_is_detect();
}

bool cdc_process_command_diagnostics(const cdc_command_t *cmd)
{
    /*
     * Diagnostics Commands
     * "GD DISP" -> Get display screenshot (multi-line response)
     *
     * "GD LMAX" -> Get maximum light duty cycle value
     * "SD LR,nnn" -> Set VIS reflection light duty cycle (nnn/LMAX) [remote]
     * "SD LT,nnn" -> Set VIS transmission light duty cycle (nnn/LMAX) [remote]
     * "SD LTU,nnn" -> Set UV transmission light duty cycle (nnn/LMAX) [remote]
     *
     * "ID S,START"   -> Invoke sensor start [remote]
     * "ID S,STOP"    -> Invoke sensor stop [remote]
     * "SD S,MODE,m"  -> Set sensor smux mode (s = [0-2]) [remote]
     * "SD S,CFG,g,t,c" -> Set sensor gain (g = [0-13]), sample time (t = [0-2047]), and sample count (c=[0-2047]) [remote]
     * "SD S,AGCEN,c" -> Enable the sensor's automatic gain control, and set AGC sample count (c=[0-2047]) [remote]
     * "SD S,AGCDIS"  -> Disable the sensor's automatic gain control [remote]
     * "GD S,READING" -> Get next sensor reading [remote]
     *
     * "ID READ,L,nnn,M,g,t,c" -> Perform controlled sensor target read [remote]
     * "ID MEAS,L,nnn" -> Perform normal density measurement read cycle [remote]
     *
     * "ID WIPE,UIDw2,CKSUM" -> Factory reset of configuration EEPROM
     *
     * "SD LOG,U" -> Set logging output to USB CDC device
     * "SD LOG,D" -> Set logging output to debug port UART
     */

    if (!cmd) { return false; }

    if (cmd->type == CMD_TYPE_GET && strcmp(cmd->action, "DISP") == 0) {
        cdc_send_command_response(cmd, "[[");
        display_capture_screenshot();
        cdc_send_response("]]\r\n");
        return true;
    } else if (cmd->type == CMD_TYPE_GET && strcmp(cmd->action, "LMAX") == 0) {
        char buf[32];
        sprintf(buf, "%d", light_get_max_value());
        cdc_send_command_response(cmd, buf);
        return true;
    } else if (cmd->type == CMD_TYPE_SET && strcmp(cmd->action, "LR") == 0 && cdc_remote_active) {
        const uint16_t light_max = light_get_max_value();
        uint16_t value = atoi(cmd->args);
        if (value > light_max) { value = light_max; }

        osStatus_t result = sensor_set_light_mode(SENSOR_LIGHT_VIS_REFLECTION, false, value);
        if (result == osOK) {
            cdc_send_command_response(cmd, "OK");
        } else {
            cdc_send_command_response(cmd, "ERR");
        }

        return true;
    } else if (cmd->type == CMD_TYPE_SET && strcmp(cmd->action, "LT") == 0 && cdc_remote_active) {
        const uint16_t light_max = light_get_max_value();
        uint16_t value = atoi(cmd->args);
        if (value > light_max) { value = light_max; }

        osStatus_t result = sensor_set_light_mode(SENSOR_LIGHT_VIS_TRANSMISSION, false, value);
        if (result == osOK) {
            cdc_send_command_response(cmd, "OK");
        } else {
            cdc_send_command_response(cmd, "ERR");
        }

        return true;
    } else if (cmd->type == CMD_TYPE_SET && strcmp(cmd->action, "LTU") == 0 && cdc_remote_active) {
        const uint16_t light_max = light_get_max_value();
        uint16_t value = atoi(cmd->args);
        if (value > light_max) { value = light_max; }

        osStatus_t result = sensor_set_light_mode(SENSOR_LIGHT_UV_TRANSMISSION, false, value);
        if (result == osOK) {
            cdc_send_command_response(cmd, "OK");
        } else {
            cdc_send_command_response(cmd, "ERR");
        }

        return true;
    } else if (strcmp(cmd->action, "S") == 0 && cdc_remote_active) {
        osStatus_t result;
        if (cmd->type == CMD_TYPE_INVOKE && strcmp(cmd->args, "START") == 0) {
            cdc_remote_sensor_active = true;
            result = sensor_start();
            if (result == osOK) {
                cdc_send_command_response(cmd, "OK");
            } else {
                cdc_send_command_response(cmd, "ERR");
            }
            return true;
        } else if (cmd->type == CMD_TYPE_INVOKE && strcmp(cmd->args, "STOP") == 0) {
            cdc_remote_sensor_active = false;
            result = sensor_stop();
            if (result == osOK) {
                cdc_send_command_response(cmd, "OK");
            } else {
                cdc_send_command_response(cmd, "ERR");
            }
            return true;
        } else if (cmd->type == CMD_TYPE_SET && strncmp(cmd->args, "MODE,", 5) == 0) {
            sensor_mode_t mode = (sensor_mode_t)atoi(cmd->args + 5);
            result = sensor_set_mode(mode);
            if (result == osOK) {
                cdc_send_command_response(cmd, "OK");
            } else {
                cdc_send_command_response(cmd, "ERR");
            }
            return true;
        } else if (cmd->type == CMD_TYPE_SET && strncmp(cmd->args, "CFG,", 4) == 0) {
            uint16_t args[3] = {0};
            size_t n = decode_u16_array_args(cmd->args + 4, args, 3);
            if (n >= 3) {
                tsl2585_gain_t gain_val = (tsl2585_gain_t)args[0];
                uint16_t sample_time = args[1];
                uint16_t sample_count = args[2];
                if (gain_val < TSL2585_GAIN_MAX && sample_time < 2048 && sample_count < 2048) {
                    result = sensor_set_config(gain_val, sample_time, sample_count);
                    if (result == osOK) {
                        cdc_send_command_response(cmd, "OK");
                    } else {
                        cdc_send_command_response(cmd, "ERR");
                    }
                    return true;
                }
            }
        } else if (cmd->type == CMD_TYPE_SET && strncmp(cmd->args, "AGCEN,", 6) == 0) {
            uint8_t sample_count = atoi(cmd->args + 6);
            if (sample_count < 2048) {
                result = sensor_set_agc_enabled(sample_count);
                if (result == osOK) {
                    cdc_send_command_response(cmd, "OK");
                } else {
                    cdc_send_command_response(cmd, "ERR");
                }
                return true;
            }
        } else if (cmd->type == CMD_TYPE_SET && strncmp(cmd->args, "AGCDIS", 6) == 0) {
            result = sensor_set_agc_disabled();
            if (result == osOK) {
                cdc_send_command_response(cmd, "OK");
            } else {
                cdc_send_command_response(cmd, "ERR");
            }
        }
        return true;
    } else if (cmd->type == CMD_TYPE_INVOKE && strcmp(cmd->action, "READ") == 0 && cdc_remote_active && !cdc_remote_sensor_active) {
        if ((cmd->args[0] == '0' || cmd->args[0] == 'R' || cmd->args[0] == 'T' || cmd->args[0] == 'U')
            && cmd->args[1] == ',') {
            uint16_t args[5] = {0};
            size_t n = decode_u16_array_args(cmd->args + 2, args, 5);
            if (n >= 5) {
                uint32_t als_reading;
                sensor_light_t light;
                uint16_t light_value = (uint16_t)args[0];
                sensor_mode_t mode = (sensor_mode_t)args[1];
                tsl2585_gain_t gain = (tsl2585_gain_t)args[2];
                uint16_t sample_time = args[3];
                uint16_t sample_count = args[4];

                if (cmd->args[0] == 'R') {
                    light = SENSOR_LIGHT_VIS_REFLECTION;
                } else if (cmd->args[0] == 'T') {
                    light = SENSOR_LIGHT_VIS_TRANSMISSION;
                } else if (cmd->args[0] == 'U') {
                    light = SENSOR_LIGHT_UV_TRANSMISSION;
                } else {
                    light = SENSOR_LIGHT_OFF;
                }

                osStatus_t result = sensor_read_target_raw(
                    light, light_value, mode, gain, sample_time, sample_count,
                    &als_reading);

                if (result == osOK) {
                    char buf[64];
                    sprintf(buf, "%lu", als_reading);
                    cdc_send_command_response(cmd, buf);
                } else {
                    cdc_send_command_response(cmd, "ERR");
                }
                return true;
            }
        }
    } else if (cmd->type == CMD_TYPE_INVOKE && strcmp(cmd->action, "MEAS") == 0 && cdc_remote_active && !cdc_remote_sensor_active) {
        if ((cmd->args[0] == 'R' || cmd->args[0] == 'T' || cmd->args[0] == 'U')
            && cmd->args[1] == ',') {
            float als_result;

            const uint16_t light_max = light_get_max_value();
            uint16_t light_value = atoi(cmd->args + 2);
            if (light_value > light_max) { light_value = light_max; }

            sensor_light_t light_source;
            if (cmd->args[0] == 'R') {
                light_source = SENSOR_LIGHT_VIS_REFLECTION;
            } else if (cmd->args[0] == 'T') {
                light_source = SENSOR_LIGHT_VIS_TRANSMISSION;
            } else if (cmd->args[0] == 'U') {
                light_source = SENSOR_LIGHT_UV_TRANSMISSION;
            } else {
                cdc_send_command_response(cmd, "ERR");
                return true;
            }

            osStatus_t result = sensor_read_target(
                light_source, light_value, &als_result, NULL, NULL);

            if (result == osOK) {
                char buf[16];
                encode_f32(buf, als_result);
                cdc_send_command_response(cmd, buf);
            } else {
                cdc_send_command_response(cmd, "ERR");
            }
            return true;
        }
    } else if (cmd->type == CMD_TYPE_INVOKE && strcmp(cmd->action, "WIPE") == 0 && cdc_remote_active) {
        char exp_buf[32];
        const app_descriptor_t *app_descriptor = app_descriptor_get();
        sprintf(exp_buf, "%08lX,%08lX",
            __bswap32(HAL_GetUIDw2()),
            __bswap32(app_descriptor->crc32));
        if (strncasecmp(exp_buf, cmd->args, sizeof(exp_buf)) == 0) {
            cdc_send_command_response(cmd, "OK");
            log_w("Factory EEPROM wipe requested");
            settings_wipe();
            osDelay(50);
            NVIC_SystemReset();
        } else {
            cdc_send_command_response(cmd, "ERR");
        }
        return true;
    } else if (cmd->type == CMD_TYPE_SET && strcmp(cmd->action, "LOG") == 0) {
        if (strcmp(cmd->args, "U") == 0) {
            cdc_send_command_response(cmd, "OK");
            cdc_logging_redirected = true;
            elog_set_text_color_enabled(false);
            elog_port_redirect(cdc_write);
            return true;
        } else if (strcmp(cmd->args, "D") == 0) {
            cdc_send_command_response(cmd, "OK");
            elog_port_redirect(NULL);
            elog_set_text_color_enabled(true);
            cdc_logging_redirected = false;
            return true;
        }
    }

    return false;
}

void cdc_send_response(const char *str)
{
    size_t len = strlen(str);
    cdc_write(str, len);
}

void cdc_send_command_response(const cdc_command_t *cmd, const char *str)
{
    char buf[128];
    char t_ch;
    char c_ch;
    if (!cmd || !str) { return; }

    switch (cmd->type) {
    case CMD_TYPE_SET:
        t_ch = 'S';
        break;
    case CMD_TYPE_GET:
        t_ch = 'G';
        break;
    case CMD_TYPE_INVOKE:
        t_ch = 'I';
        break;
    default:
        return;
    }

    switch (cmd->category) {
    case CMD_CATEGORY_SYSTEM:
        c_ch = 'S';
        break;
    case CMD_CATEGORY_MEASUREMENT:
        c_ch = 'M';
        break;
    case CMD_CATEGORY_CALIBRATION:
        c_ch = 'C';
        break;
    case CMD_CATEGORY_DIAGNOSTICS:
        c_ch = 'D';
        break;
    default:
        return;
    }

    size_t n = snprintf(buf, sizeof(buf), "%c%c %s,%s\r\n", t_ch, c_ch, cmd->action, str);
    cdc_write(buf, n);
}

void cdc_send_density_reading(char prefix, float d_value, float d_zero, float raw_value)
{
    float d_display;
    char buf[16];
    char sign;

    /* Force any invalid values to be zero */
    if (isnan(d_value) || isinf(d_value)) {
        d_value = 0.0F;
    }
    if (isnan(raw_value) || isinf(raw_value)) {
        raw_value = 0.0F;
    }

    /* Calculate the display value */
    if (!isnan(d_zero)) {
        d_display = d_value - d_zero;
    } else {
        d_display = d_value;
    }

    /* Find the sign character */
    if (d_display >= 0.0F) {
        sign = '+';
    } else {
        sign = '-';
    }

    /* Format the result */
    size_t n = sprintf_(buf, "%c%c%.2fD\r\n", prefix, sign, fabsf(d_display));

    /* Catch cases where a negative was rounded to zero */
    if (strncmp(buf + 1, "-0.00", 5) == 0) {
        buf[1] = '+';
    }

    if (reading_format == READING_FORMAT_EXT) {
        char extbuf[48];
        n -= 2;
        strncpy(extbuf, buf, n);
        extbuf[n++] = ',';
        n += encode_f32(extbuf + n, d_value);
        extbuf[n++] = ',';
        n += encode_f32(extbuf + n, d_zero);
        extbuf[n++] = ',';
        n += encode_f32(extbuf + n, raw_value);
        extbuf[n++] = '\r';
        extbuf[n++] = '\n';
        extbuf[n] = '\0';
        cdc_write(extbuf, n);
    } else {
        cdc_write(buf, n);
    }
}

void cdc_send_raw_sensor_reading(const sensor_reading_t *reading)
{
    if (!cdc_remote_sensor_active || !reading) { return; }

    static const cdc_command_t cmd = {
        .type = CMD_TYPE_GET,
        .category = CMD_CATEGORY_DIAGNOSTICS,
        .action = "S"
    };
    char buf[64];

    sprintf(buf, "%lu,%d,%d,%d",
        reading->mod0.als_data, reading->mod0.gain, reading->sample_time, reading->sample_count);
    cdc_send_command_response(&cmd, buf);
}

void cdc_send_remote_state(bool enabled)
{
    osMutexAcquire(cdc_mutex, portMAX_DELAY);
    cdc_remote_active = enabled && cdc_remote_enabled;
    cdc_remote_sensor_active = false;
    osMutexRelease(cdc_mutex);
    cdc_command_t cmd = {
        .type = CMD_TYPE_INVOKE,
        .category = CMD_CATEGORY_SYSTEM,
        .action = "REMOTE"
    };
    cdc_send_command_response(&cmd, enabled ? "1" : "0");
}

void cdc_write(const char *buf, size_t len)
{
    osMutexAcquire(cdc_mutex, portMAX_DELAY);
    if (cdc_host_connected && len > 0) {
        uint32_t n = 0;
        uint32_t offset = 0;
        do {
            n = tud_cdc_write(buf + offset, len - offset);
            if (n == 0) {
                if (!cdc_logging_redirected) {
                    log_w("Write error");
                }
                break;
            }
            tud_cdc_write_flush();
            offset += n;

            if (osSemaphoreAcquire(cdc_tx_semaphore, CDC_TX_TIMEOUT) != osOK) {
                if (!cdc_logging_redirected) {
                    log_e("Unable to acquire cdc_tx_semaphore");
                }
                tud_cdc_write_clear();
                tud_cdc_abort_transfer();
                cdc_set_connected(false);
                break;
            }
        } while (offset < len);
    }
    osMutexRelease(cdc_mutex);
}

size_t encode_f32_array_response(char *buf, const float *array, size_t len)
{
    size_t offset = 0;
    for (size_t i = 0; i < len; i++) {
        if (i > 0) {
            buf[offset++] = ',';
        }
        offset += encode_f32(buf + offset, array[i]);
    }
    buf[offset] = '\0';
    return offset;
}

size_t encode_f32(char *out, float value)
{
    uint8_t buf[4];
    memset(buf, 0, sizeof(buf));
    copy_from_f32(buf, value);
    return sprintf(out, "%02X%02X%02X%02X", buf[0], buf[1], buf[2], buf[3]);
}

uint8_t decode_hex_char(char ch, bool *ok)
{
    uint8_t val;
    bool valid = true;
    if ('0' <= ch && ch <= '9') {
        val = (uint8_t)(ch - '0');
    } else if ('A' <= ch && ch <= 'F') {
        val = (uint8_t)(ch - 'A' + 10);
    } else if ('a' <= ch && ch <= 'f') {
        val = (uint8_t)(ch - 'a' + 10);
    } else {
        val = 0;
        valid = false;
    }
    if (ok) { *ok = valid; }
    return val;
}

float decode_f32(const char *buf)
{
    uint8_t hexbuf[4];
    uint8_t nib1;
    uint8_t nib2;
    bool ok;

    if (strlen(buf) != 8) {
        return NAN;
    }

    for (size_t i = 0; i < 8; i += 2) {
        nib1 = decode_hex_char(buf[i], &ok);
        if (!ok) { return NAN; }

        nib2 = decode_hex_char(buf[i + 1], &ok);
        if (!ok) { return NAN; }

        hexbuf[i / 2] = (nib1 << 4) + nib2;
    }

    return copy_to_f32(hexbuf);
}

size_t decode_f32_array_args(const char *args, float *elements, size_t len)
{
    char numbuf[16];
    size_t n = 0;
    size_t p, q;

    p = 0;
    q = p;
    while (n < len) {
        if (args[q] == ',' || args[q] == '\0') {
            if (p >= q) { break; }
            if (q - p < sizeof(numbuf) - 1) {
                memset(numbuf, 0, sizeof(numbuf));
                strncpy(numbuf, args + p, q - p);
                elements[n] = decode_f32(numbuf);
            } else {
                elements[n] = NAN;
            }
            n++;
            if (args[q] == '\0') {
                break;
            } else {
                p = q + 1;
                q = p;
            }
        } else {
            q++;
        }
    }

    return n;
}

size_t decode_u16_array_args(const char *args, uint16_t *elements, size_t len)
{
    char numbuf[16];
    size_t n = 0;
    size_t p, q;

    p = 0;
    q = p;
    while (n < len) {
        if (args[q] == ',' || args[q] == '\0') {
            if (p >= q) { break; }
            if (q - p < sizeof(numbuf) - 1) {
                memset(numbuf, 0, sizeof(numbuf));
                strncpy(numbuf, args + p, q - p);
                elements[n] = atoi(numbuf);
            } else {
                elements[n] = 0;
            }
            n++;
            if (args[q] == '\0') {
                break;
            } else {
                p = q + 1;
                q = p;
            }
        } else {
            q++;
        }
    }

    return n;
}
