dektronics/printalyzer-uvdensitometer/software/firmware/src/app_descriptor.h

#ifndef APP_DESCRIPTOR_H
#define APP_DESCRIPTOR_H

#include <stdint.h>

#define APP_DESCRIPTOR_MAGIC_WORD 0xABCD7105

/**
 * Application descriptor structure.
 *
 * Note: The memory layout of this structure is not allowed to change,
 * because it is also handled by the bootloader and the build scripts.
 */
typedef struct {
    uint32_t magic_word;        /*!< Magic word APP_DESCRIPTOR_MAGIC_WORD */
    uint32_t reserved1[3];      /*!< Reserved */
    char project_name[32];      /*!< Project name */
    char version[32];           /*!< Application version */
    char build_date[20];        /*!< Build timestamp */
    char build_describe[64];    /*!< Build Git description */
    uint32_t reserved2[22];     /*!< Reserved */
    uint32_t crc32;             /*!< CRC-32 checksum using the STM32F4 hardware algorithm */
} app_descriptor_t;

#ifndef __CDT_PARSER__
_Static_assert(sizeof(app_descriptor_t) == 256, "app_descriptor_t should be 256 bytes");
#endif

/**
 * Gets the application descriptor for the active firmware image.
 *
 * This structure is stored at a specific location within flash, and
 * can only be updated as part of the build process.
 */
const app_descriptor_t *app_descriptor_get();

#endif /* APP_DESCRIPTOR_H */
