dektronics/printalyzer-uvdensitometer/software/firmware/src/display_assets.h

#ifndef DISPLAY_ASSETS_H
#define DISPLAY_ASSETS_H

#include <stdint.h>

typedef struct {
    const uint8_t *bits;
    const uint16_t width;
    const uint16_t height;
} asset_info_t;

typedef enum {
    ASSET_REFLECTION_ICON_40 = 0,
    ASSET_REFLECTION_ICON_40_1,
    ASSET_REFLECTION_ICON_40_2,
    ASSET_TRANSMISSION_ICON_40,
    ASSET_TRANSMISSION_ICON_40_1,
    ASSET_TRANSMISSION_ICON_40_2,
    ASSET_VIS_ICON,
    ASSET_UV_ICON,
    ASSET_ZERO_INDICATOR,
    ASSET_MAX
} asset_name_t;

uint8_t display_asset_get(asset_info_t *asset_info, asset_name_t asset_name);

#endif /* DISPLAY_ASSETS_H */
